MostlyWithinSpec/Network-Goblin-ND-2/docs/images/tdr-dongle-bottom.png

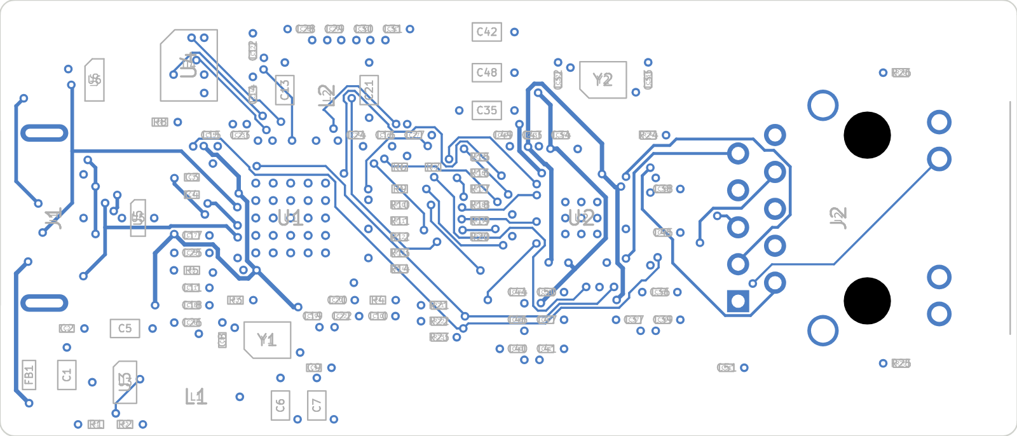
docs/images/tdr-dongle-bottom.png
